JOQUR/DESIGNLABORATORY22-23/GameSW/Core/Src/gpio.c

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

/* Includes ------------------------------------------------------------------*/
#include "gpio.h"

/* USER CODE BEGIN 0 */
#include "player.h"
#include "debug_settings.h"
/* USER CODE END 0 */

/*----------------------------------------------------------------------------*/
/* Configure GPIO                                                             */
/*----------------------------------------------------------------------------*/
/** Configure pins as
        * Analog
        * Input
        * Output
        * EVENT_OUT
        * EXTI
     PA2   ------> USART2_TX
     PA15 (JTDI)   ------> USART2_RX
*/
void MX_GPIO_Init(void)
{

  GPIO_InitTypeDef GPIO_InitStruct = {0};

  /* GPIO Ports Clock Enable */
  __HAL_RCC_GPIOC_CLK_ENABLE();
  __HAL_RCC_GPIOA_CLK_ENABLE();
  __HAL_RCC_GPIOB_CLK_ENABLE();

  /*Configure GPIO pin Output Level */
  HAL_GPIO_WritePin(GPIOA, PIR_OUT_1_Pin|PIR_OUT_2_Pin|BUZZER_Pin|BABA_JAGA_PATRZY_Pin
                          |GAME_ON_Pin, GPIO_PIN_RESET);

  /*Configure GPIO pin : PtPin */
  GPIO_InitStruct.Pin = VCP_TX_Pin;
  GPIO_InitStruct.Mode = GPIO_MODE_AF_PP;
  GPIO_InitStruct.Pull = GPIO_NOPULL;
  GPIO_InitStruct.Speed = GPIO_SPEED_FREQ_VERY_HIGH;
  GPIO_InitStruct.Alternate = GPIO_AF7_USART2;
  HAL_GPIO_Init(VCP_TX_GPIO_Port, &GPIO_InitStruct);

  /*Configure GPIO pins : PAPin PAPin PAPin PAPin
                           PAPin */
  GPIO_InitStruct.Pin = PIR_OUT_1_Pin|PIR_OUT_2_Pin|BUZZER_Pin|BABA_JAGA_PATRZY_Pin
                          |GAME_ON_Pin;
  GPIO_InitStruct.Mode = GPIO_MODE_OUTPUT_PP;
  GPIO_InitStruct.Pull = GPIO_NOPULL;
  GPIO_InitStruct.Speed = GPIO_SPEED_FREQ_LOW;
  HAL_GPIO_Init(GPIOA, &GPIO_InitStruct);

  /*Configure GPIO pins : PBPin PBPin PBPin PBPin */
  GPIO_InitStruct.Pin = PIR_SIG_1_Pin|PIR_SIG_2_Pin|BUTTON_1_Pin|BUTTON_2_Pin;
  GPIO_InitStruct.Mode = GPIO_MODE_IT_RISING;
  GPIO_InitStruct.Pull = GPIO_NOPULL;
  HAL_GPIO_Init(GPIOB, &GPIO_InitStruct);

  /*Configure GPIO pin : PtPin */
  GPIO_InitStruct.Pin = VCP_RX_Pin;
  GPIO_InitStruct.Mode = GPIO_MODE_AF_PP;
  GPIO_InitStruct.Pull = GPIO_NOPULL;
  GPIO_InitStruct.Speed = GPIO_SPEED_FREQ_VERY_HIGH;
  GPIO_InitStruct.Alternate = GPIO_AF3_USART2;
  HAL_GPIO_Init(VCP_RX_GPIO_Port, &GPIO_InitStruct);

  /* EXTI interrupt init*/
  HAL_NVIC_SetPriority(EXTI0_IRQn, 0, 0);
  HAL_NVIC_EnableIRQ(EXTI0_IRQn);

  HAL_NVIC_SetPriority(EXTI1_IRQn, 0, 0);
  HAL_NVIC_EnableIRQ(EXTI1_IRQn);

  HAL_NVIC_SetPriority(EXTI3_IRQn, 0, 0);
  HAL_NVIC_EnableIRQ(EXTI3_IRQn);

  HAL_NVIC_SetPriority(EXTI4_IRQn, 0, 0);
  HAL_NVIC_EnableIRQ(EXTI4_IRQn);

}

/* USER CODE BEGIN 2 */
void HAL_GPIO_EXTI_Callback(uint16_t GPIO_Pin)
{
	if (GPIO_Pin == PIR_SIG_2_Pin)
	{
		/* Blink red diode */
		player_two.score = 1;
	}
	else if (GPIO_Pin == PIR_SIG_1_Pin)
	{
		/* Blink yellow diode */
		player_one.score = 1;
	}
	else if (GPIO_Pin == BUTTON_1_Pin)
	{
		player_one.score = 1;
	}
	else if (GPIO_Pin == BUTTON_2_Pin)
	{
		player_two.score = 1;
	}
}
/* USER CODE END 2 */
